xinanhuang/SCOUT_LiDAR/CAD/motor_encoder_mount/gear0.SLDPRT

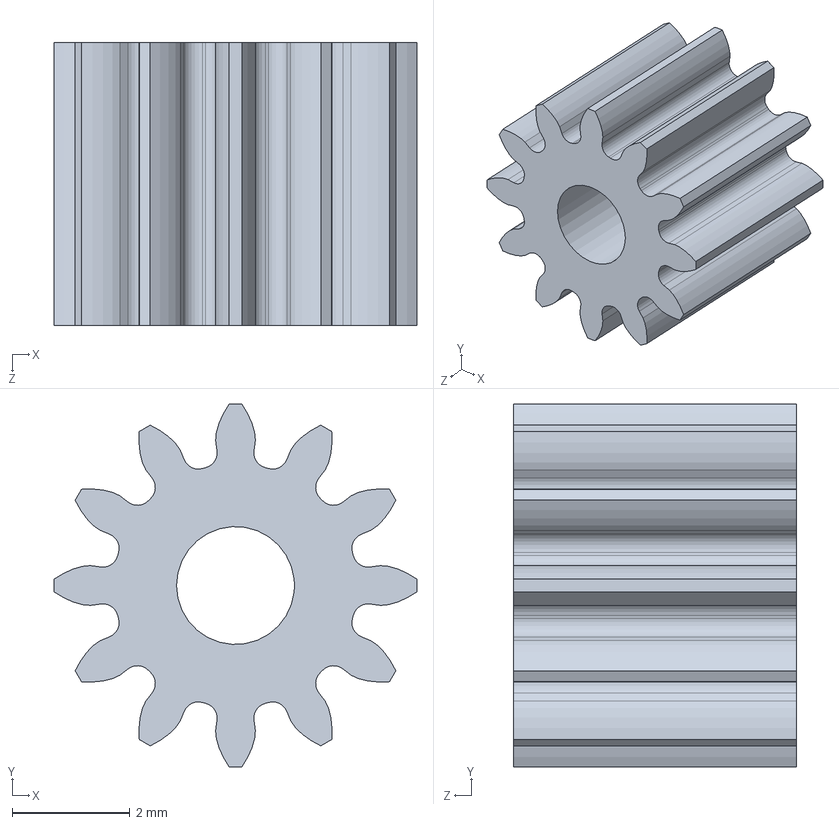
[picture p29: CAD file, 2020-08-04]
CAD/motor_encoder_mount/gear0.SLDPRT
6.16 x 6.16 x 4.80 mm
