xinanhuang/SCOUT_LiDAR/CAD/stepper_encoder.SLDPRT

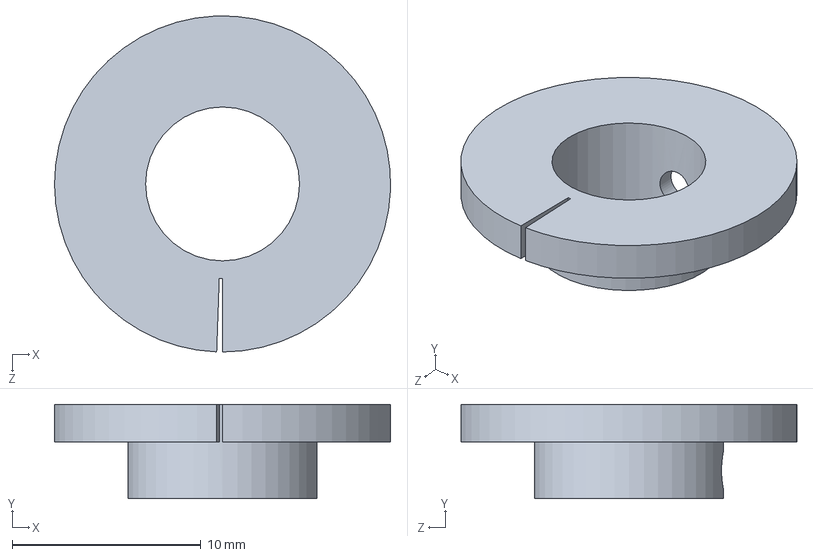
[picture p30: CAD file, 2020-08-04]
CAD/stepper_encoder.SLDPRT
17.8 x 5.00 x 17.8 mm
