xinanhuang/SCOUT_LiDAR/CAD/STL/lidar_rotation_stage - rotating_disk-3 rotating_disk_stepper_arm-1.STL

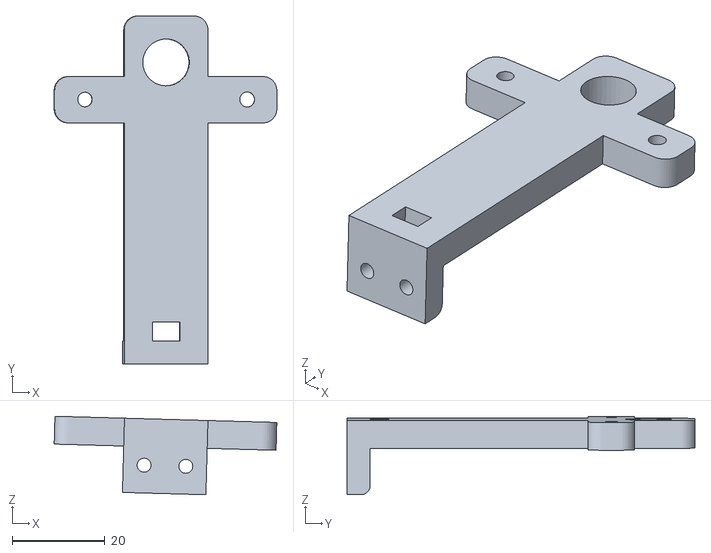
[picture p31: CAD file, 2020-08-04]
CAD/STL/lidar_rotation_stage - rotating_disk-3 rotating_disk_stepper_arm-1.STL
48.0 x 75.0 x 16.9
