xinanhuang/SCOUT_LiDAR/CAD/axial_design/rotating_sturt.SLDPRT

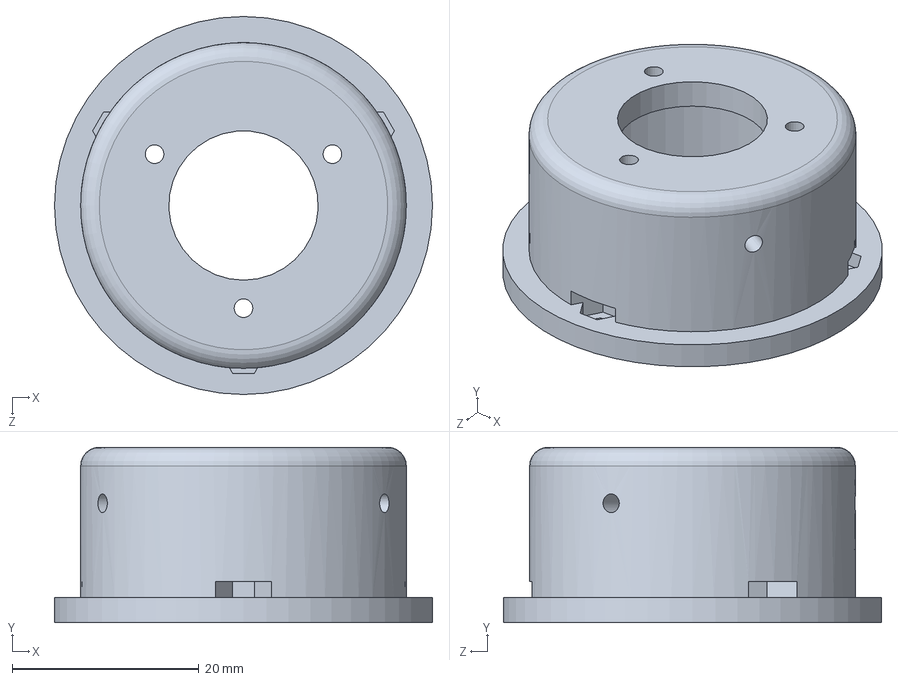
[picture p32: CAD file, 2020-08-04]
CAD/axial_design/rotating_sturt.SLDPRT
40.5 x 18.8 x 40.5 mm
