xinanhuang/SCOUT_LiDAR/CAD/motor_encoder_mount/rod2.SLDPRT

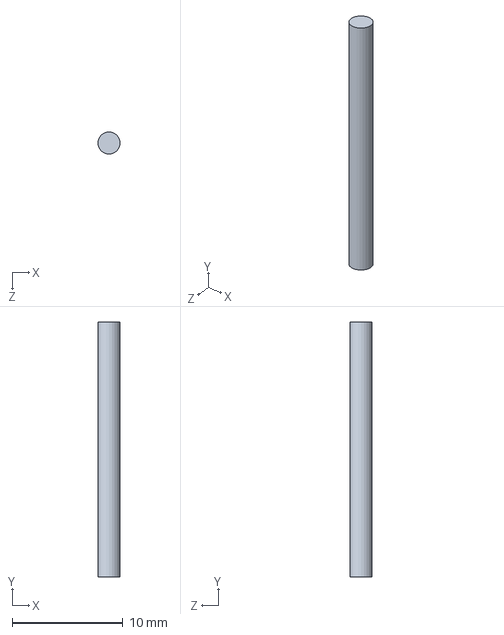
[picture p33: CAD file, 2020-08-04]
CAD/motor_encoder_mount/rod2.SLDPRT
2.00 x 23.0 x 2.00 mm
