xinanhuang/SCOUT_LiDAR/CAD/sf30c.SLDPRT

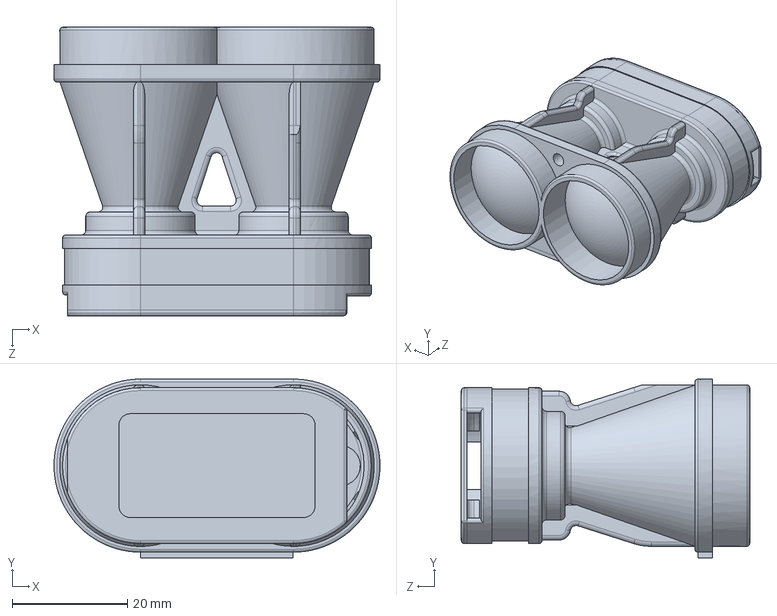
[picture p34: CAD file, 2020-08-04]
CAD/sf30c.SLDPRT
56.5 x 31.0 x 50.0 mm
