xinanhuang/SCOUT_LiDAR/CAD/axial_design/slipring_base.SLDPRT

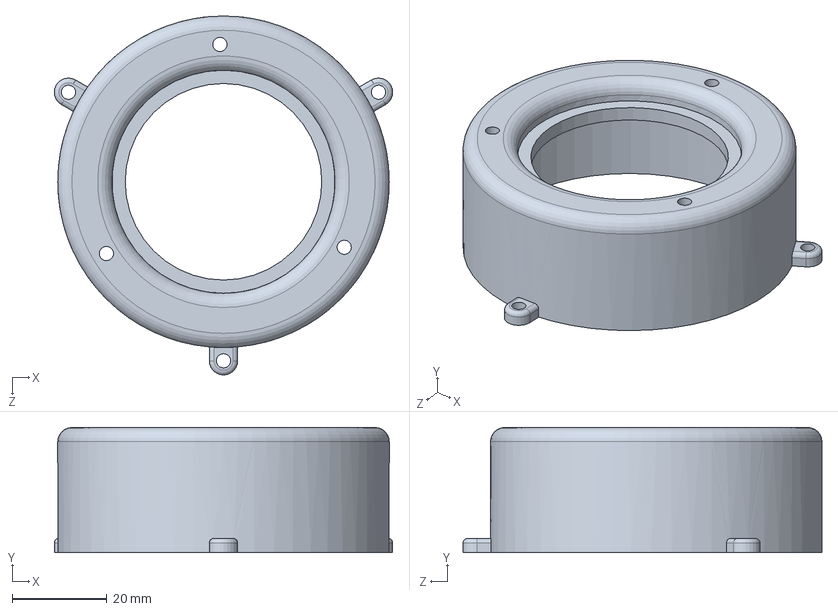
[picture p35: CAD file, 2020-08-04]
CAD/axial_design/slipring_base.SLDPRT
71.5 x 26.4 x 75.8 mm
