xinanhuang/SCOUT_LiDAR/CAD/rotating_disk_encoder_arm.SLDPRT

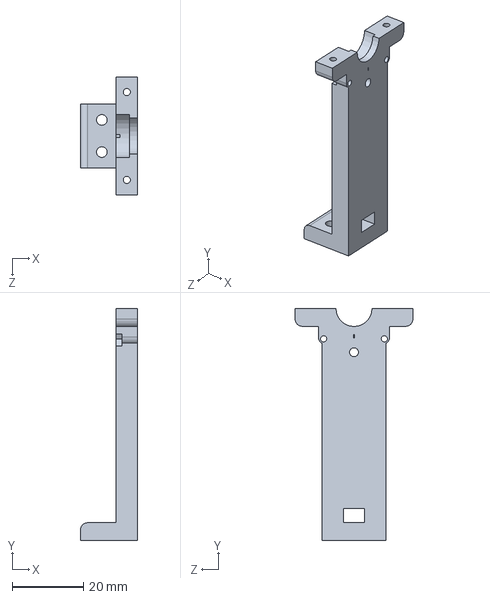
[picture p36: CAD file, 2020-08-04]
CAD/rotating_disk_encoder_arm.SLDPRT
16.0 x 65.0 x 33.0 mm
