xinanhuang/SCOUT_LiDAR/CAD/axial_design/lock_disk.SLDPRT

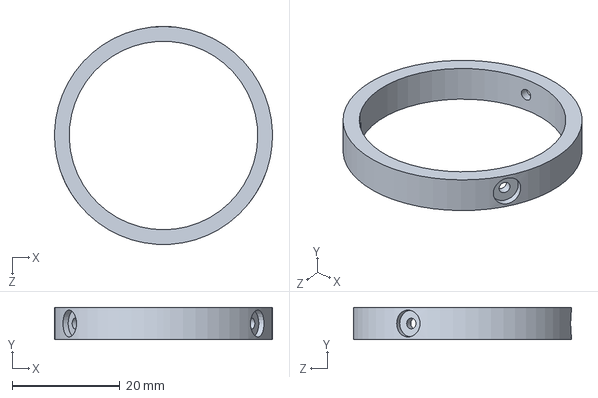
[picture p37: CAD file, 2020-08-04]
CAD/axial_design/lock_disk.SLDPRT
40.5 x 6.00 x 40.5 mm
