xinanhuang/SCOUT_LiDAR/CAD/ball_bearing_lidar.SLDPRT

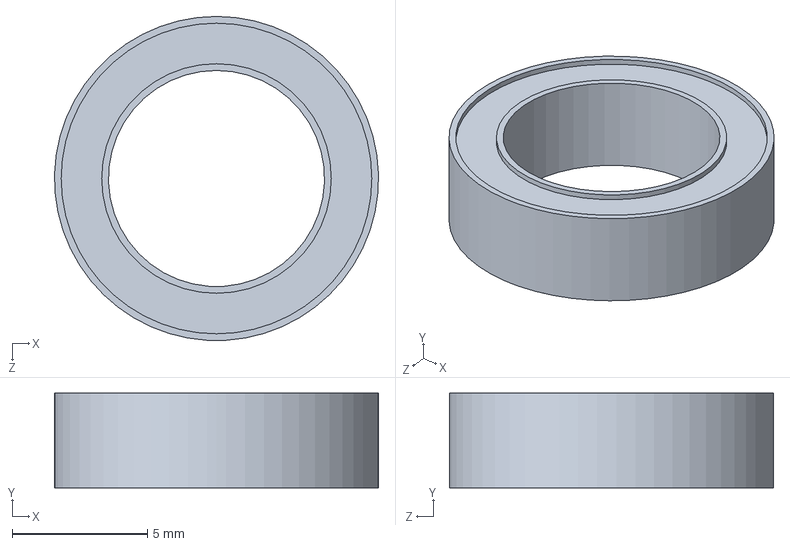
[picture p38: CAD file, 2020-08-04]
CAD/ball_bearing_lidar.SLDPRT
12.0 x 3.50 x 12.0 mm
