xinanhuang/SCOUT_LiDAR/CAD/motor_encoder_mount/gear2.SLDPRT

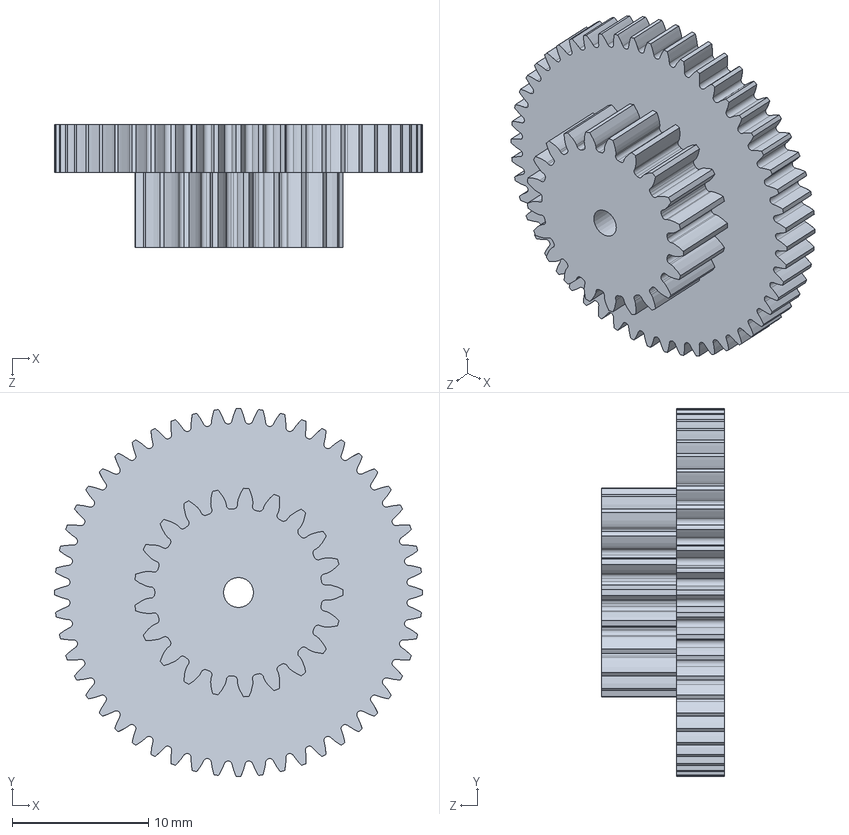
[picture p39: CAD file, 2020-08-04]
CAD/motor_encoder_mount/gear2.SLDPRT
27.0 x 27.0 x 9.00 mm
