xinanhuang/SCOUT_LiDAR/CAD/STL/lidar_rotation_stage - rotating_disk-3 SF30 _attachemnt-1.STL

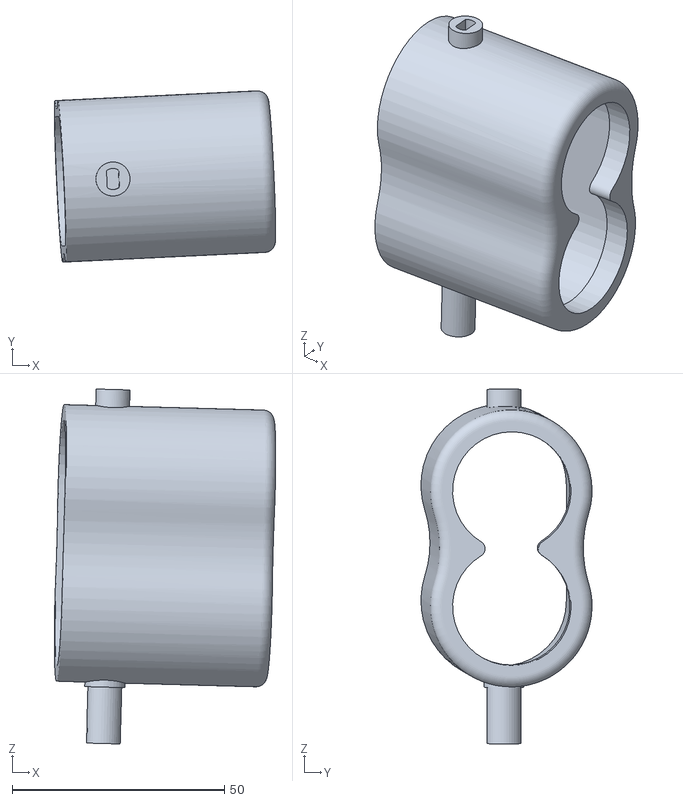
[picture p40: CAD file, 2020-08-04]
CAD/STL/lidar_rotation_stage - rotating_disk-3 SF30 _attachemnt-1.STL
52.2 x 40.3 x 83.6
