xinanhuang/SCOUT_LiDAR/CAD/motor_encoder_mount/gear_plate.SLDPRT

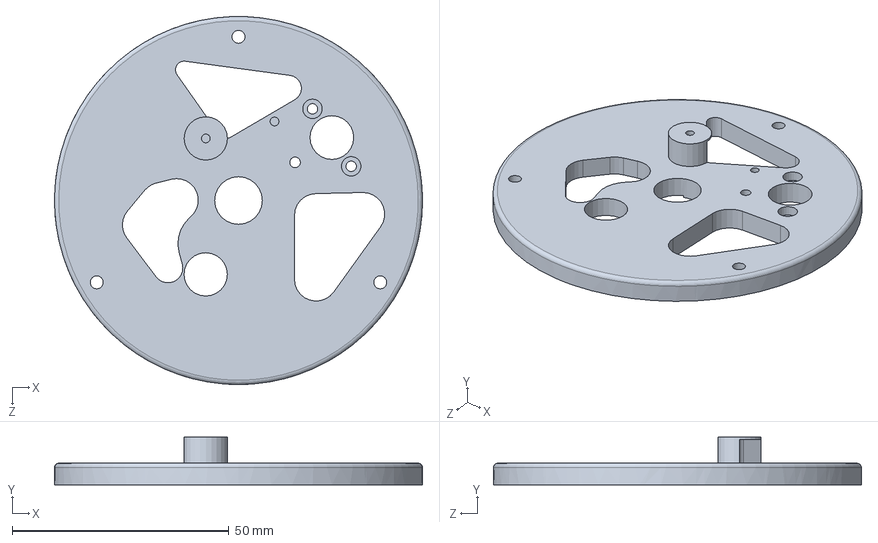
[picture p41: CAD file, 2020-08-04]
CAD/motor_encoder_mount/gear_plate.SLDPRT
85.0 x 11.0 x 85.0 mm
