xinanhuang/SCOUT_LiDAR/CAD/rotating_disk_base.SLDPRT

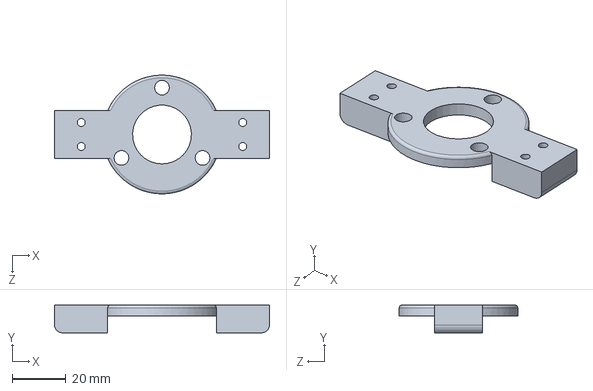
[picture p42: CAD file, 2020-08-04]
CAD/rotating_disk_base.SLDPRT
80.4 x 10.4 x 44.4 mm
