xinanhuang/SCOUT_LiDAR/CAD/STL/lidar_rotation_stage - rotating_disk-3 Step - 28BYJ-48-1.STL

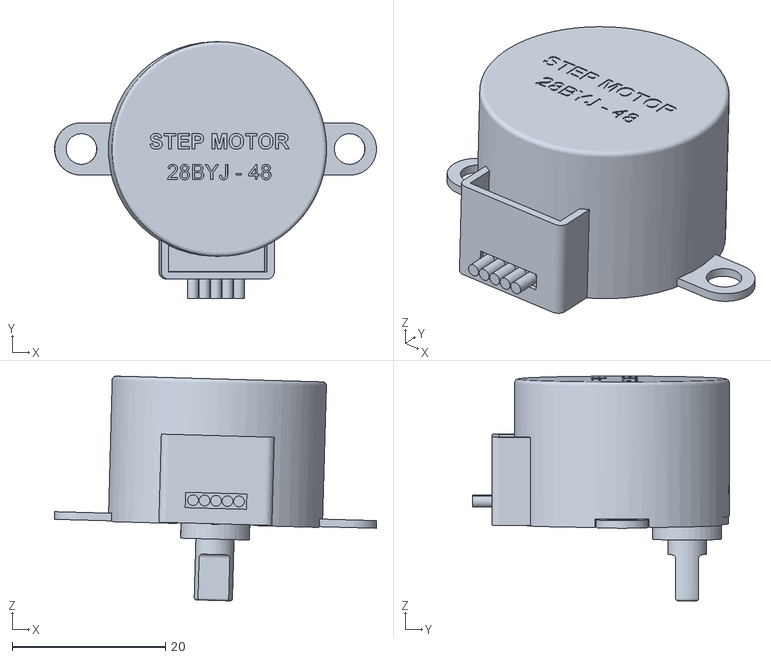
[picture p43: CAD file, 2020-08-04]
CAD/STL/lidar_rotation_stage - rotating_disk-3 Step - 28BYJ-48-1.STL
42.0 x 33.5 x 29.3
