xinanhuang/SCOUT_LiDAR/CAD/rotating_disk_stepper_arm.SLDPRT

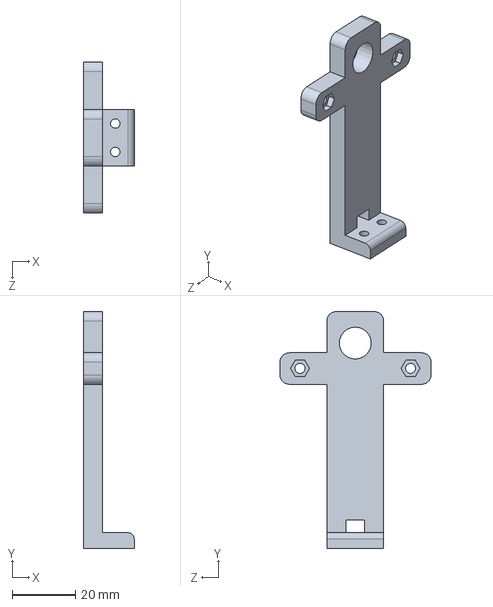
[picture p44: CAD file, 2020-08-04]
CAD/rotating_disk_stepper_arm.SLDPRT
16.0 x 75.0 x 47.8 mm
