xinanhuang/SCOUT_LiDAR/CAD/motor_encoder_mount/motor.SLDPRT

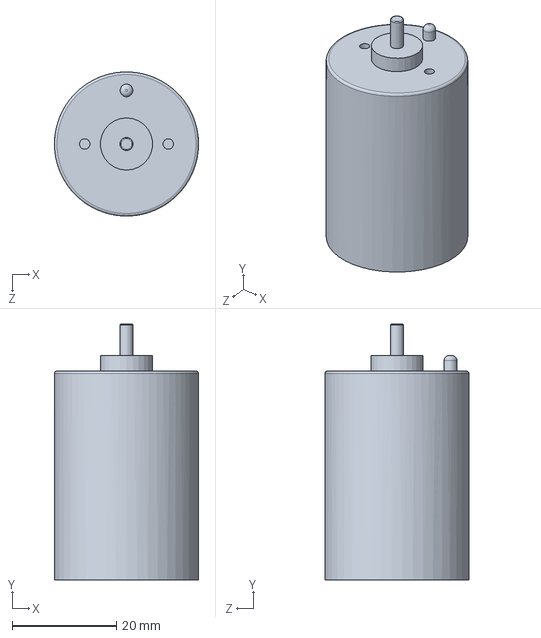
[picture p45: CAD file, 2020-08-04]
CAD/motor_encoder_mount/motor.SLDPRT
27.6 x 49.0 x 27.6 mm
