xinanhuang/SCOUT_LiDAR/CAD/slipring.SLDPRT

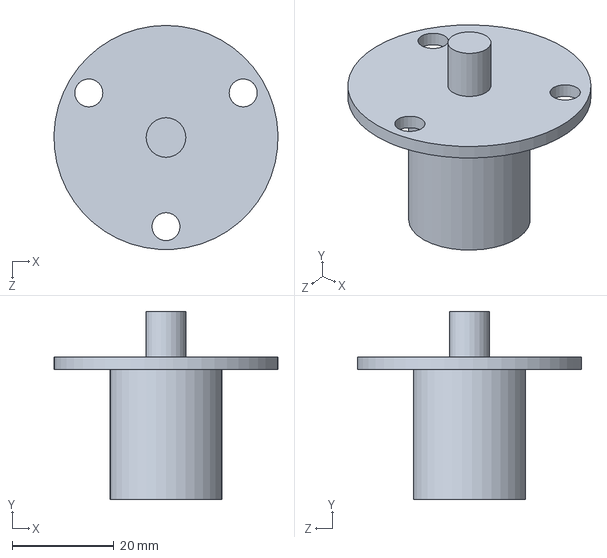
[picture p46: CAD file, 2020-08-04]
CAD/slipring.SLDPRT
44.0 x 37.0 x 44.0 mm
