xinanhuang/SCOUT_LiDAR/CAD/motor_encoder_mount/gearv3 v1.SLDPRT

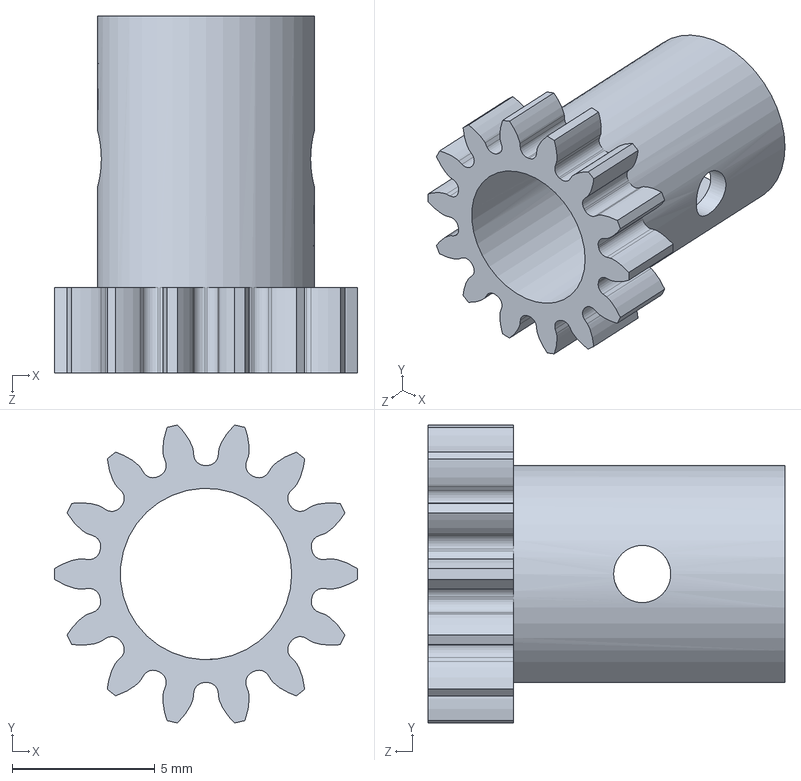
[picture p47: CAD file, 2020-08-04]
CAD/motor_encoder_mount/gearv3 v1.SLDPRT
10.6 x 10.4 x 12.5 mm
