xinanhuang/SCOUT_LiDAR/CAD/rotating_disk_bearing_holder.SLDPRT

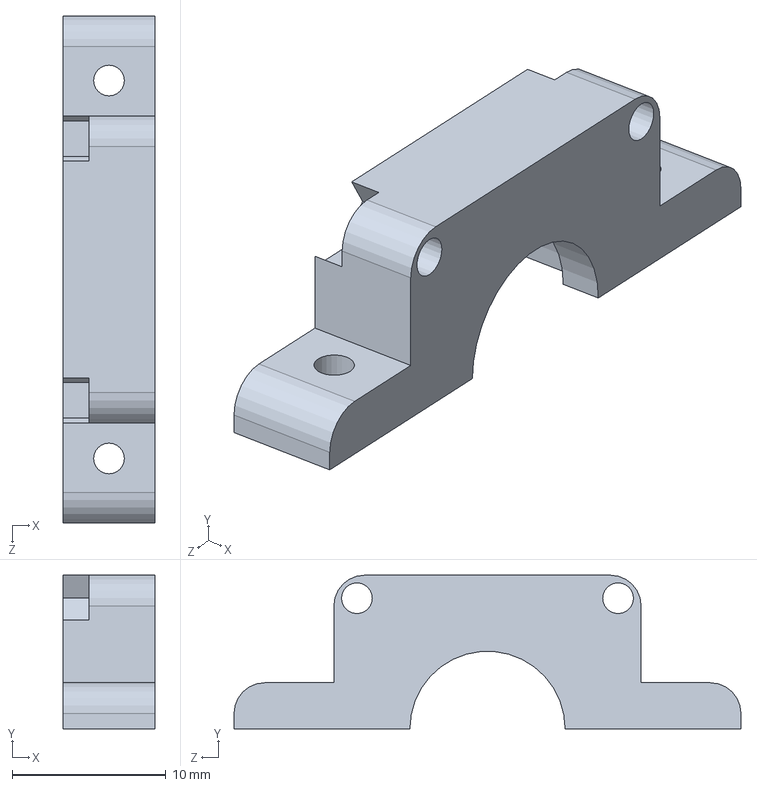
[picture p48: CAD file, 2020-08-04]
CAD/rotating_disk_bearing_holder.SLDPRT
6.00 x 10.0 x 33.0 mm
