xinanhuang/SCOUT_LiDAR/CAD/STL/lidar_rotation_stage - single_bearing-1 slipring_base-1.STL

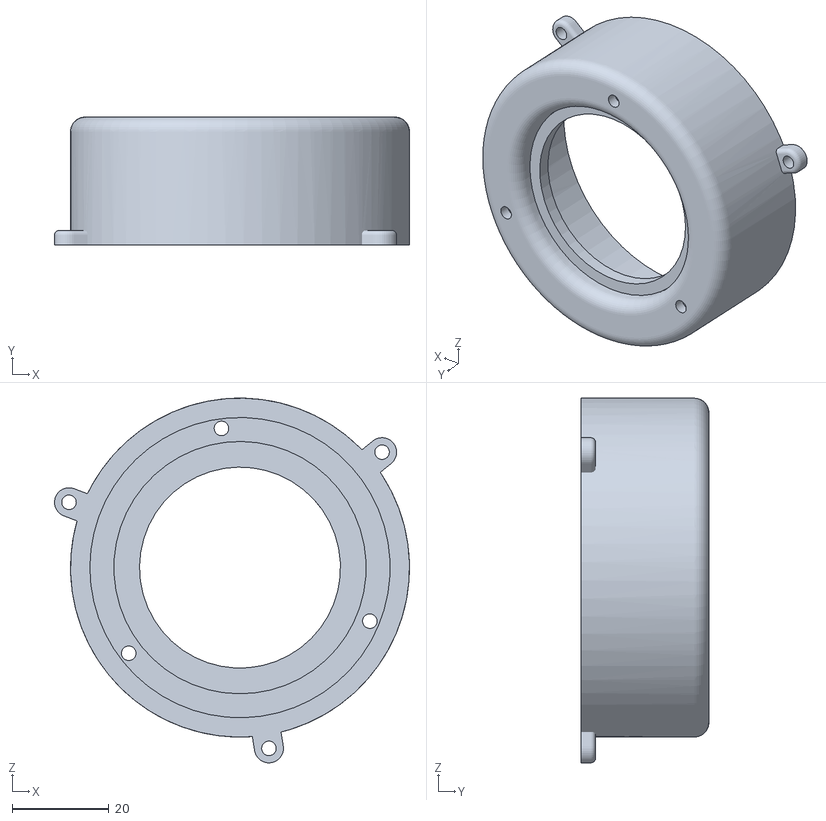
[picture p49: CAD file, 2020-08-04]
CAD/STL/lidar_rotation_stage - single_bearing-1 slipring_base-1.STL
73.3 x 26.4 x 75.3
