xinanhuang/SCOUT_LiDAR/CAD/SF10 _attachemnt.SLDPRT

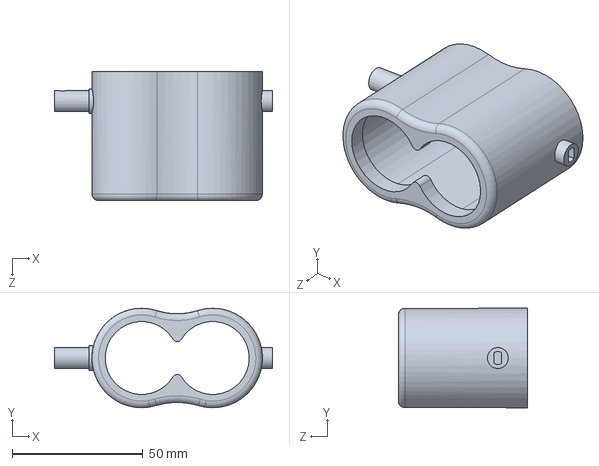
[picture p50: CAD file, 2020-08-04]
CAD/SF10 _attachemnt.SLDPRT
83.5 x 38.1 x 49.5 mm
