xinanhuang/SCOUT_LiDAR/CAD/STL/lidar_rotation_stage - rotating_disk-3 stepper_encoder_case-1.STL

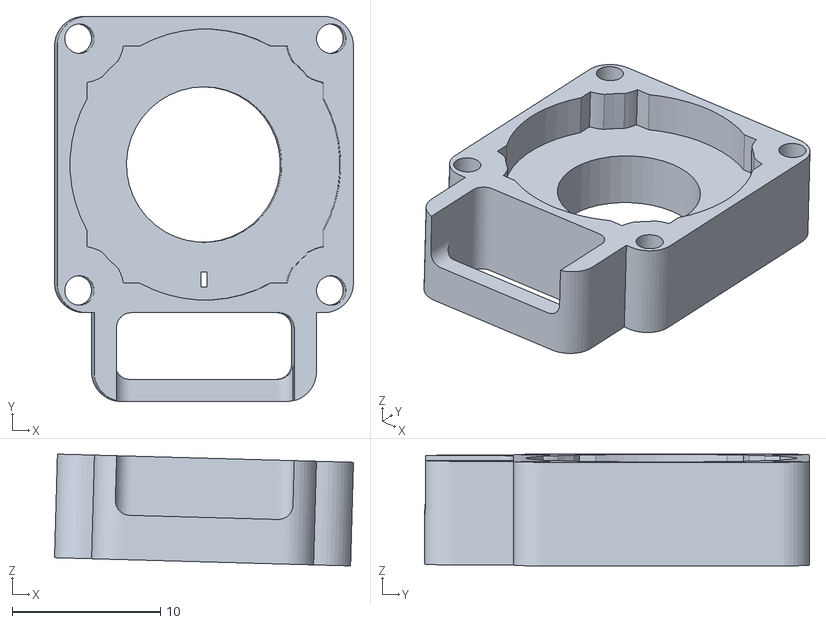
[picture p51: CAD file, 2020-08-04]
CAD/STL/lidar_rotation_stage - rotating_disk-3 stepper_encoder_case-1.STL
20.2 x 26.0 x 7.55
