xinanhuang/SCOUT_LiDAR/CAD/motor_encoder_mount/rod1.SLDPRT

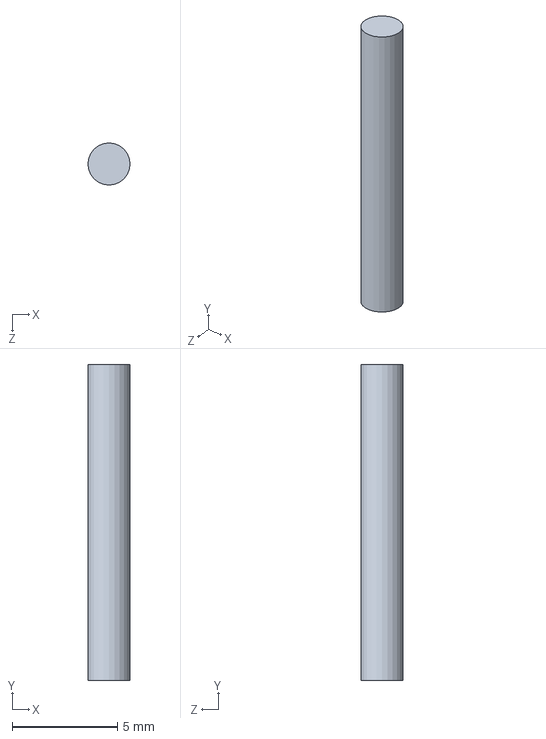
[picture p52: CAD file, 2020-08-04]
CAD/motor_encoder_mount/rod1.SLDPRT
2.00 x 15.0 x 2.00 mm
