xinanhuang/SCOUT_LiDAR/CAD/rotating_disk_adptr.SLDPRT

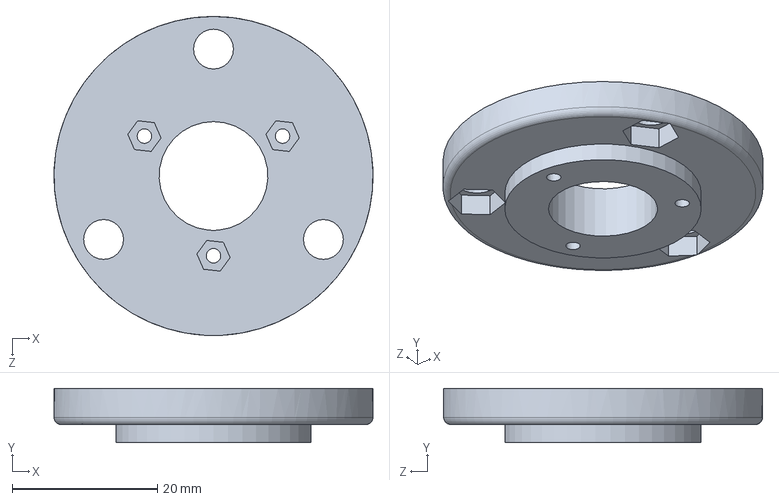
[picture p53: CAD file, 2020-08-04]
CAD/rotating_disk_adptr.SLDPRT
44.0 x 7.50 x 44.0 mm
