xinanhuang/SCOUT_LiDAR/CAD/STL/lidar_rotation_stage - rotating_disk-3 rotating_disk_bearing_holder-1.STL

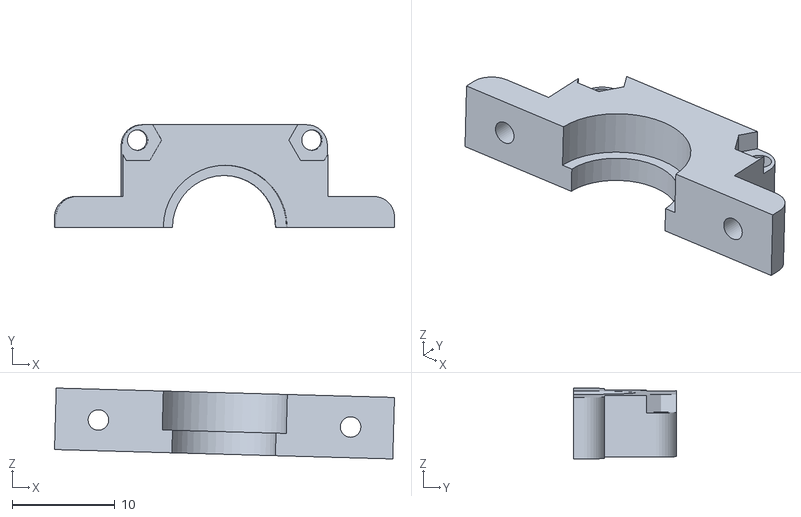
[picture p54: CAD file, 2020-08-04]
CAD/STL/lidar_rotation_stage - rotating_disk-3 rotating_disk_bearing_holder-1.STL
33.2 x 10.0 x 6.91
