xinanhuang/SCOUT_LiDAR/CAD/motor_encoder_mount/gear3 v2.SLDPRT

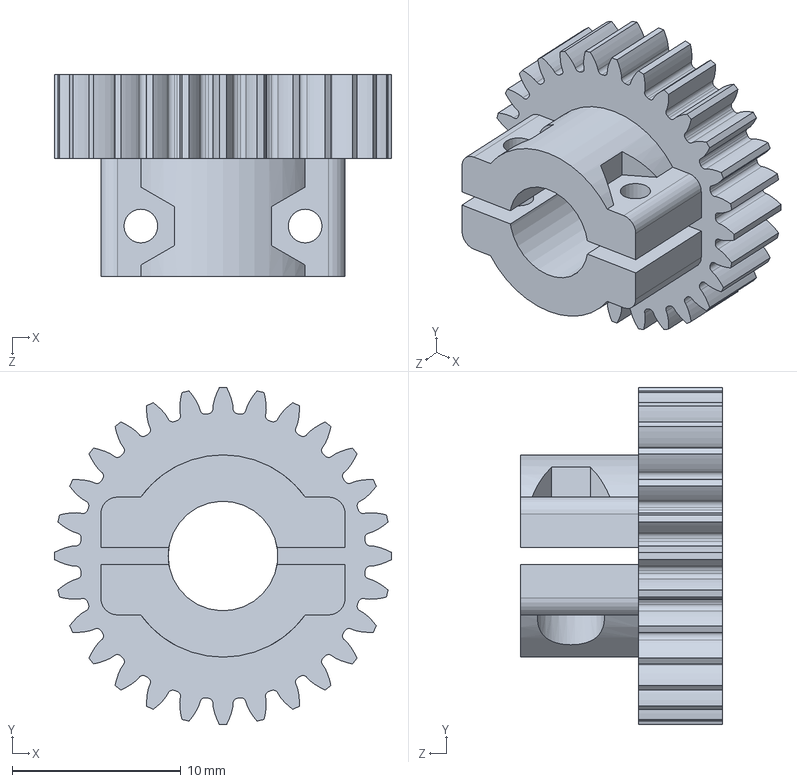
[picture p55: CAD file, 2020-08-04]
CAD/motor_encoder_mount/gear3 v2.SLDPRT
20.0 x 20.0 x 12.0 mm
