xinanhuang/SCOUT_LiDAR/CAD/stepper_encoder_case.SLDPRT

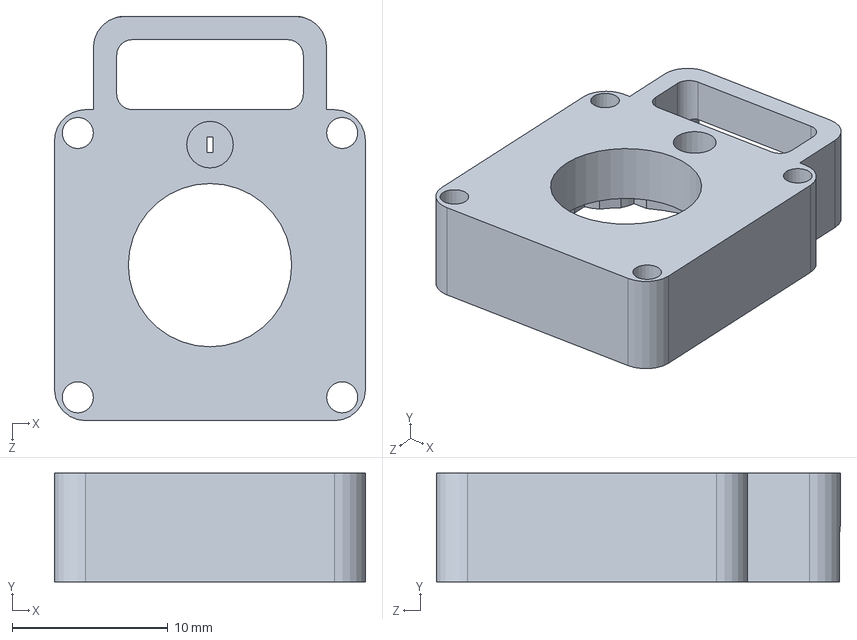
[picture p56: CAD file, 2020-08-04]
CAD/stepper_encoder_case.SLDPRT
20.0 x 7.00 x 26.0 mm
