xinanhuang/SCOUT_LiDAR/CAD/STL/lidar_rotation_stage - rotating_disk-3 stepper_encoder_case_cap-1.STL

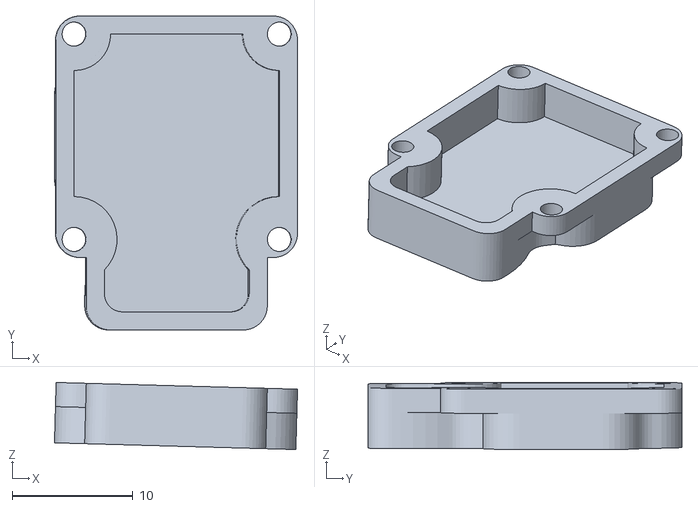
[picture p57: CAD file, 2020-08-04]
CAD/STL/lidar_rotation_stage - rotating_disk-3 stepper_encoder_case_cap-1.STL
20.1 x 26.0 x 5.55
