xinanhuang/SCOUT_LiDAR/CAD/stepper_encoder_case_cap.SLDPRT

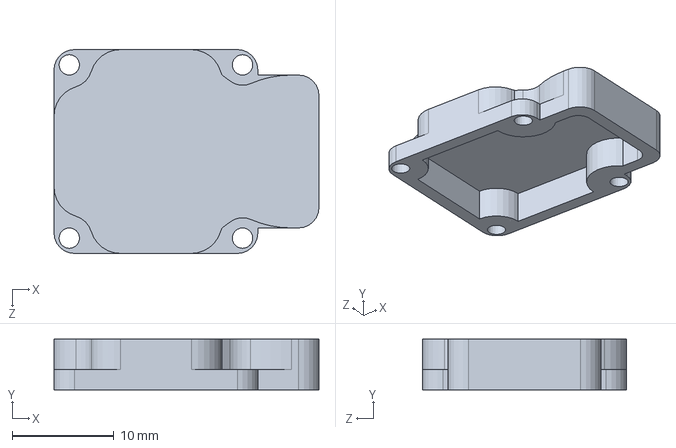
[picture p58: CAD file, 2020-08-04]
CAD/stepper_encoder_case_cap.SLDPRT
26.0 x 5.00 x 20.0 mm
