xinanhuang/SCOUT_LiDAR/CAD/STL/lidar_rotation_stage - rotating_disk-3 rotating_disk_base-1.STL

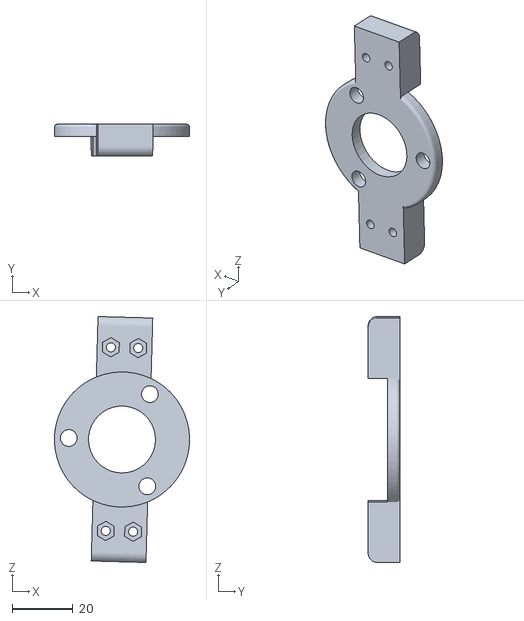
[picture p59: CAD file, 2020-08-04]
CAD/STL/lidar_rotation_stage - rotating_disk-3 rotating_disk_base-1.STL
44.4 x 10.4 x 80.8
