xinanhuang/SCOUT_LiDAR/CAD/STL/lidar_rotation_stage - rotating_disk-3 stepper_encoder-1.STL

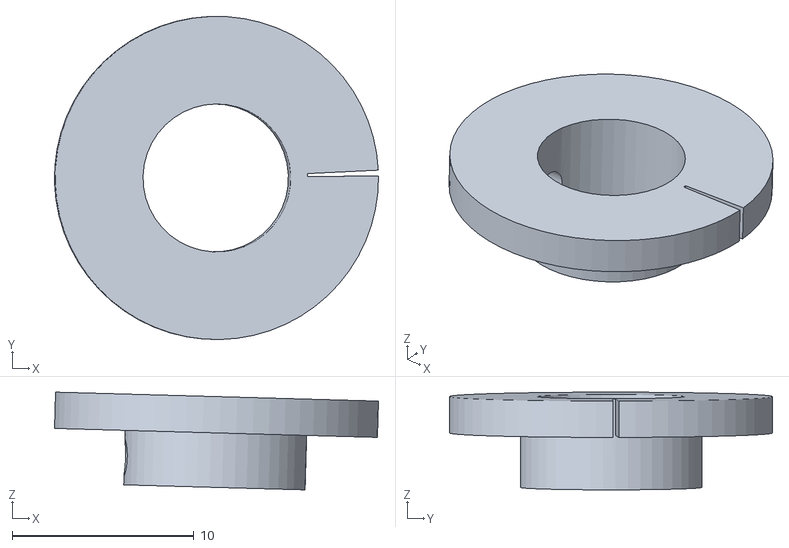
[picture p60: CAD file, 2020-08-04]
CAD/STL/lidar_rotation_stage - rotating_disk-3 stepper_encoder-1.STL
17.8 x 17.8 x 5.38
